Solartraveler/audiomux/src-device/Src/femtoVsnprintf.c

/*
Copyright 2021 Malte Marwedel

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
1. Redistributions of source code must retain the above copyright notice, this
 list of conditions and the following disclaimer.

2. Redistributions in binary form must reproduce the above copyright notice,
 this list of conditions and the following disclaimer in the documentation
 and/or other materials provided with the distribution.

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
Changelog:
2021-02-14: Version 1.0


*/

#include <stdint.h>
#include <stdarg.h>
#include <string.h>
#include <ctype.h>
#include <stdbool.h>

#ifdef TEST_PC
#include <stdio.h>
#endif

#include "femtoVsnprintf.h"

/*
	Supported formats:
	%c
	%s
	%u
	%X
	%Wu where W is in the range 1...9
	%WX where W is in the range 1...9
	%W0u where W is in the range 1...9
	%W0X where W is in the range 1...9
The output is always \0 terminated
*/

#if defined(FEMTO_SUPPORT_DECIMAL) || defined(FEMTO_SUPPORT_HEX)

//converted, but chars in reverse order
static size_t utoaReversed(unsigned int value, char * out, size_t outLen, unsigned int radix)
{
	size_t i;
	for (i = 0; i < outLen - 1; i++)
	{
		if (value == 0)
		{
			break;
		}
		unsigned int digit = value % radix;
		value /= radix;
		if (digit > 9)
		{
			digit += 'A' - 10;
		}
#ifdef FEMTO_SUPPORT_HEX
		else
		{
			digit += '0';
		}
#endif
		out[i] = digit;
	}
	if (i == 0)
	{
		out[i] = '0';
		i++;
	}
	out[i] = '\0';
	return i;
}
#endif

void femtoVsnprintf(char * output, size_t outLen, const char * format, va_list args)
{
	while (outLen > 1)
	{
		char input = *format;
		format++;
		if (input == '\0')
		{
			break;
		}
		if (input == '%')
		{
			input = *format;
			if (input == '\0')
			{
				break;
			}
			format++;
#ifdef FEMTO_SUPPORT_C
			if (input == 'c')
			{
				unsigned int x = va_arg(args, int);
				*output = x;
				output++;
				outLen--;
			}
#endif
#ifdef FEMTO_SUPPORT_S
			if (input == 's')
			{
				const char * strIn = va_arg(args, char *);
				while ((strIn) && (*strIn) && (outLen > 1))
				{
					*output = *strIn;
					output++;
					strIn++;
					outLen--;
				}
			}
#endif
#if defined(FEMTO_SUPPORT_C) || defined(FEMTO_SUPPORT_S)
			else
#endif
			{
				unsigned int x = va_arg(args, int);
				uint8_t minWidht = 0;
#ifdef FEMTO_SUPPORT_LEADINGZEROS
				bool leadingZeros = false;
#endif
				if (isdigit(input))
				{
					minWidht = input - '0'; //single digit conversion
					input = *format;
					if (input == '\0')
					{
						break;
					}
					format++;
#ifdef FEMTO_SUPPORT_LEADINGZEROS
					if (minWidht == 0) //leading zeros
					{
						minWidht = input - '0'; //single digit conversion
						input = *format;
						if (input == '\0')
						{
							break;
						}
						format++;
						leadingZeros = true;
					}
#endif
				}
				char buffer[11];
				size_t len = 0;
				if (input == 'u')
				{
					len = utoaReversed(x, buffer, sizeof(buffer), 10);
				}
#ifdef FEMTO_SUPPORT_HEX
				else
				{
					len = utoaReversed(x, buffer, sizeof(buffer), 16);
				}
#endif
				size_t resultLen = len;
				while ((resultLen < minWidht) && (outLen > 1)) //fill leading spaces/zeros
				{
#ifdef FEMTO_SUPPORT_LEADINGZEROS
					if (leadingZeros) {
						*output = '0';
					}
					else
#endif
					{
						*output = ' ';
					}
					output++;
					resultLen++;
					outLen--;
				}
				for (size_t i = 0; i < len; i++)
				{
					if (outLen <= 1)
					{
						break;
					}
					*output = buffer[len - i - 1];
					output++;
					outLen--;
				}
			}
		} else
		{
			*output = input;
			output++;
			outLen--;
		}
	}
	if (outLen)
	{
		*output = '\0';
	}
	va_end(args);
}

#ifdef FEMTO_SUPPORT_SNPRINTF
void femtoSnprintf(char * output, size_t outLen, const char * format, ...) {
	va_list args;
	va_start(args, format);
	femtoVsnprintf(output, outLen, format, args);
	va_end(args);
}
#endif

#ifdef TEST_PC

void testMe(const char * format, ...) {
	va_list args;
	va_start(args, format);
	char buffer[128];
	femtoVsnprintf(buffer, 128, format, args);
	printf(buffer);
}

int main(void) {
	testMe("Hello World\n");
	testMe("A char: >%c<\n", 'X');
	const char * teststring = "More Hello";
	testMe("A string: >%s<\n", teststring);
	testMe("A decimal number: >%u<\n", 1234567890);
	testMe("A decimal zero: >%u<\n", 0);
	testMe("A hex number: >%X<\n", 0xFEDCBA98);
	testMe("A decimal number 4 chars wide: >%4u<\n", 42);
	testMe("A hex number 8 chars wide: >%8X<\n", 0xABC);
	testMe("Decimal leading zeros: >%06u<\n", 665);

	return 0;
}

#endif
